Reikimen/CASA0019-SDV-Group-Storm/Image/Assert/eara-Photoroom.png

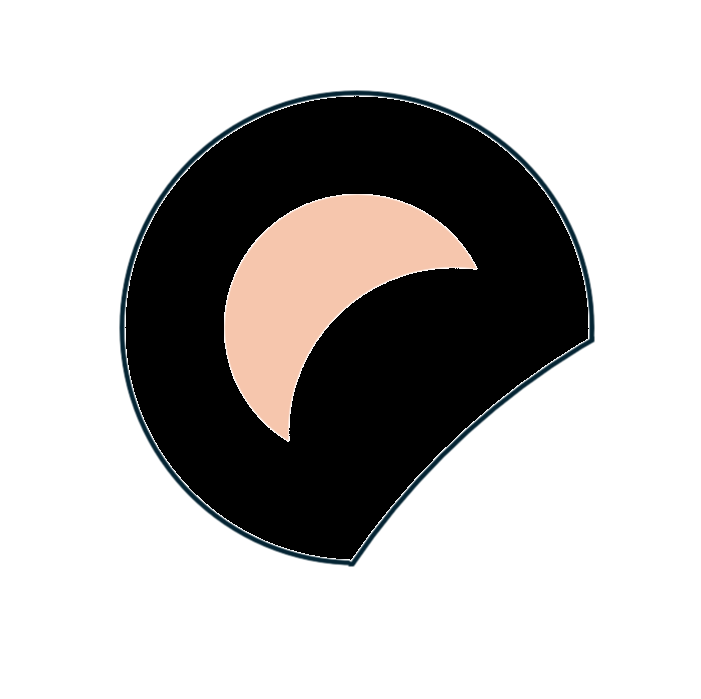
Image/Assert/eara-Photoroom.png
