Reikimen/CASA0019-SDV-Group-Storm/Image/Assert/LCD2004.png

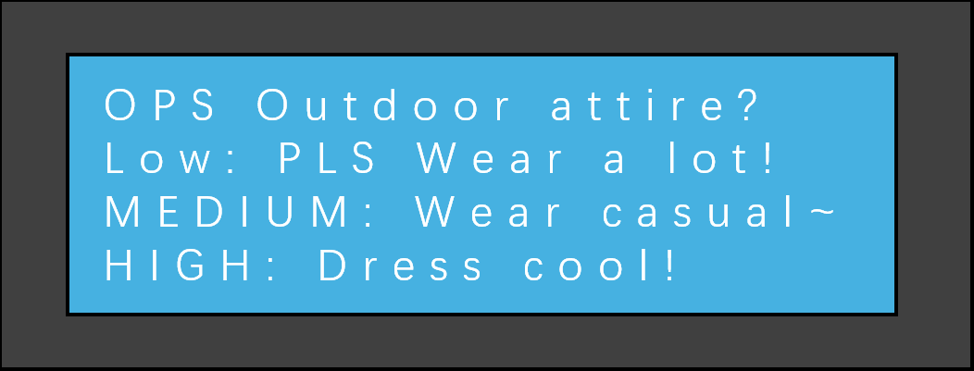
Image/Assert/LCD2004.png
